loggerhead-instruments/amx/Arduino/amx/cmd.ino

#define CMD(a,b) ( a + (b << 8))
#define TRUE 1
#define FALSE 0

int ProcCmd(char *pCmd)
{
  short *pCV;
  short n;
  long lv1, lv2;
  char s[22];
        unsigned int tday;
        unsigned int tmonth;
        unsigned int tyear;
        unsigned int thour;
        unsigned int tmin;
        unsigned int tsec;

  pCV = (short*)pCmd;

  n = strlen(pCmd);
  if(n<2) 
          return TRUE;

  switch(*pCV)
  {                     
    // IMU
    case ('I' + ('M'<<8)):
    {
      sscanf(&pCmd[3],"%d",&lv1);
      imu_srate = lv1;
      fileType = 1;
      imuFlag = 1;
      break;
    }

  // Accelerometer full scale
    case ('A' + ('G'<<8)):
    {
      sscanf(&pCmd[3],"%d",&lv1);
      accel_scale = lv1;
      break;
    }

  // Hydrophone sensitivity if not default -180
    case ('H' + ('C'<<8)):
    {
      sscanf(&pCmd[3],"%d",&lv1);
      hydroCal = lv1;
      break;
    }

    // Keller Pressure and Temperature
    case ('K' + ('P'<<8)):
    {
      pressure_sensor = 2;
      fileType = 1;
      break;
    }

    // Measurement Specialities Pressure and Temperature
    case ('M' + ('P'<<8)):
    {
      pressure_sensor = 1;
      fileType = 1;
      break;
    }

    // RGB light sensor setup
    case ('L' + ('S'<<8)):
    {
      rgbFlag = 1;
      fileType = 1;
      break;
    }

    // Disable LEDs
    case ('L' + ('D'<<8)):
    {
      LEDSON = 0;
      break;
    }
    
    // Enable bright LED
    case ('B' + ('L'<<8)):
    {
      briteFlag = 1;
    }

    // Set of Real Time Clock
    case ('T' + ('M'<<8)):
    {
         //set time
         sscanf(&pCmd[3],"%d-%d-%d %d:%d:%d",&tyear,&tmonth,&tday,&thour,&tmin,&tsec);
         setTeensyTime(thour, tmin, tsec, tday, tmonth, tyear + 2000);
         Serial.print("Clock Set (now): ");
         Serial.println(now());
         Serial.print("Clock set (getTeensyTime): ");
         Serial.println(getTeensy3Time());
         break;
      }

    case ('B' + ('W'<<8)):
    {
         //set time
         sscanf(&pCmd[3],"%d-%d-%d %d:%d:%d",&tyear,&tmonth,&tday,&thour,&tmin,&tsec);
         tmElements_t NewTime;
         NewTime.Second = tsec;
         NewTime.Minute = tmin;
         NewTime.Hour = thour;
         NewTime.Day = tday;
         NewTime.Month = tmonth;
         NewTime.Year = tyear + 2000 - 1970;
         burnTime = makeTime(NewTime); // makeTime is offset from 1970
         burnFlag = 1;
         Serial.print("Burn Time:");
         Serial.println(burnTime);
         break;
      }

    // Burn Minutes (burn set number of minutes after start)
    case ('B' + ('M'<<8)):
    {
         sscanf(&pCmd[3],"%d",&lv1);
         burnMinutes = lv1;
         burnFlag = 2;
         break;
      }

      case ('N' + ('D'<<8)):
      {
        noDC = 1;
        break;
      }

    case ('D' + ('I'<<8)):
      {
        printDiags = 1;
        break;
      }
      
      case ('R' + ('D'<<8)):
      {
        sscanf(&pCmd[3],"%d",&lv1);
        rec_dur = lv1;
        break;
      }
      
      case ('R' + ('I'<<8)):
      {
        sscanf(&pCmd[3],"%d",&lv1);
        rec_int = lv1;
        break;
      } 

      case ('S' + ('G'<<8)):
      {
        sscanf(&pCmd[3],"%d",&lv1);
        systemGain = lv1;
        break;
      } 

    case ('D' + ('S'<<8)):
    {
      sscanf(&pCmd[3],"%d:%d",&lv1, &lv2);
      delayStartHours = lv1;
      delayStartMinutes = lv2;
      break;
    }  


    //default nPlayBackFiles = 0; // number of playback files
    case ('P' + ('F'<<8)):
    {
      sscanf(&pCmd[3],"%d",&lv1);
      nPlayBackFiles = lv1;
      break;
    }
    //default minPlayBackInterval = 120; // keep playbacks from being closer than x seconds
    case ('P' + ('I'<<8)):
    {
      sscanf(&pCmd[3],"%d",&lv1);
      minPlayBackInterval = lv1;
      break;
    }
    //default longestPlayback = 30; // longest file for playback, used to power down playback board
    case ('P' + ('D'<<8)):
    {
      sscanf(&pCmd[3],"%d",&lv1);
      longestPlayback = lv1;
      break;
    }
    //default playBackDepthThreshold = 10.0; // tag must go deeper than this depth to trigger threshold
    case ('P' + ('T'<<8)):
    {
      sscanf(&pCmd[3],"%d",&lv1);
      playBackDepthThreshold = lv1;
      break;
    }
    //default ascentDepthTrigger = 5.0; // after exceed playBackDepthThreshold, must ascend this amount to trigger playback
    case ('P' + ('A'<<8)):
    {
      sscanf(&pCmd[3],"%d",&lv1);
      ascentDepthTrigger = lv1;
      break;
    }
    //default playBackResetDepth = 2.0; // tag needs to come back above this depth before next playback can happen
    case ('P' + ('R'<<8)):
    {
      sscanf(&pCmd[3],"%d",&lv1);
      playBackResetDepth = lv1;
      break;
    }
    //default maxPlayBacks = 20; // tag needs to come back above this depth before next playback can happen
    case ('P' + ('M'<<8)):
    {
      sscanf(&pCmd[3],"%d",&lv1);
      maxPlayBacks = lv1;
      break;
    }
    // default simulateDepth = 0
    case ('S' + ('D'<<8)):
    {
      simulateDepth = 1;
      break;
    }
    
  } 
  return TRUE;
}

boolean LoadScript()
{
  char s[30];
  char c;
  short i;
  int j = 0;

  File file;
  unsigned long TM_byte;
  int comment_TM = 0;

  // Read card setup.txt file to set date and time, recording interval
  file=SD.open("setup.txt");
 if(file)
 {
   do{
        i = 0;
        s[i] = 0;
        do{
            c = file.read();
            if(c!='\r') s[i++] = c;
            if((c=='T') & (i==1)) 
            {
              TM_byte = file.position() - 1;
              comment_TM = 1;
            }
            if(i>29) break;
          }while(c!='\n');
          s[--i] = 0;
          if(s[0] != '/' && i>1)
          {
            ProcCmd(s);
          }
      }while(file.available());
      file.close();  
      
      // comment out TM line if it exists
      if (comment_TM)
      {
        Serial.print("Comment TM ");
        Serial.println(TM_byte);
        file = SD.open("setup.txt", FILE_WRITE);
        file.seek(TM_byte);
        file.print("//");
        file.close();
      }
      
  }
  else
  {   
    Serial.println("setup.txt not opened");

   // display.println("no setup file");
    return 0;
  }

  // Read simulated depth file
  file = SD.open("depth.txt");
  Serial.println("Depth file");
  if(file){
    do{
      j = 0;
      do{ // scan next line
        c = file.read();
        if(c!='\r') s[j] = c;
        j++;
        if(j>29) break;
      }while(c!='\n');
      Serial.print(c);
      sscanf(s,"%f",&depthProfile[i]);
      Serial.print(i); Serial.print(" ");
      Serial.print(depthProfile[i]);
      i++;
      if(i==60) break;
    }while(file.available());
    file.close();
  }
  
 return 1;  
}
