loggerhead-instruments/amx/Arduino/amx/ISL29125.ino

// Some code from Sparkfun  https://github.com/sparkfun/SparkFun_ISL29125_Breakout_Arduino_Library/tree/master/src

int _addr = 0x44;

// ISL29125 Registers
#define DEVICE_ID 0x00
#define CONFIG_1 0x01
#define CONFIG_2 0x02
#define CONFIG_3 0x03
#define THRESHOLD_LL 0x04
#define THRESHOLD_LH 0x05
#define THRESHOLD_HL 0x06
#define THRESHOLD_HH 0x07
#define STATUS 0x08 
#define GREEN_L 0x09 
#define GREEN_H 0x0A
#define RED_L 0x0B
#define RED_H 0x0C
#define BLUE_L 0x0D
#define BLUE_H 0x0E

// Configuration Settings
#define CFG_DEFAULT 0x00

// CONFIG1
// Pick a mode, determines what color[s] the sensor samples, if any
#define CFG1_MODE_POWERDOWN 0x00
#define CFG1_MODE_G 0x01
#define CFG1_MODE_R 0x02
#define CFG1_MODE_B 0x03
#define CFG1_MODE_STANDBY 0x04
#define CFG1_MODE_RGB 0x05
#define CFG1_MODE_RG 0x06
#define CFG1_MODE_GB 0x07

// Light intensity range
// In a dark environment 375Lux is best, otherwise 10KLux is likely the best option
#define CFG1_375LUX 0x00
#define CFG1_10KLUX 0x08

// Change this to 12 bit if you want less accuracy, but faster sensor reads
// At default 16 bit, each sensor sample for a given color is about ~100ms
#define CFG1_16BIT 0x00
#define CFG1_12BIT 0x10

// Unless you want the interrupt pin to be an input that triggers sensor sampling, leave this on normal
#define CFG1_ADC_SYNC_NORMAL 0x00
#define CFG1_ADC_SYNC_TO_INT 0x20

// CONFIG2
// Selects upper or lower range of IR filtering
#define CFG2_IR_OFFSET_OFF 0x00
#define CFG2_IR_OFFSET_ON 0x80

// Sets amount of IR filtering, can use these presets or any value between 0x00 and 0x3F
// Consult datasheet for detailed IR filtering calibration
#define CFG2_IR_ADJUST_LOW 0x00
#define CFG2_IR_ADJUST_MID 0x20
#define CFG2_IR_ADJUST_HIGH 0x3F

// CONFIG3
// No interrupts, or interrupts based on a selected color
#define CFG3_NO_INT 0x00
#define CFG3_G_INT 0x01
#define CFG3_R_INT 0x02
#define CFG3_B_INT 0x03

// How many times a sensor sample must hit a threshold before triggering an interrupt
// More consecutive samples means more times between interrupts, but less triggers from short transients
#define CFG3_INT_PRST1 0x00
#define CFG3_INT_PRST2 0x04
#define CFG3_INT_PRST4 0x08
#define CFG3_INT_PRST8 0x0C

// If you would rather have interrupts trigger when a sensor sampling is complete, enable this
// If this is disabled, interrupts are based on comparing sensor data to threshold settings
#define CFG3_RGB_CONV_TO_INT_DISABLE 0x00
#define CFG3_RGB_CONV_TO_INT_ENABLE 0x10

// STATUS FLAG MASKS
#define FLAG_INT 0x01
#define FLAG_CONV_DONE 0x02
#define FLAG_BROWNOUT 0x04
#define FLAG_CONV_G 0x10
#define FLAG_CONV_R 0x20
#define FLAG_CONV_B 0x30

bool islInit(){
  Serial.println("Light init"); 
  bool ret = true;
  ret = config(CFG1_MODE_RGB | CFG1_10KLUX, CFG2_IR_ADJUST_HIGH, CFG_DEFAULT); 
  return ret;
}

bool islSleep(){
  bool ret = true;
  ret = config(CFG1_MODE_POWERDOWN, CFG2_IR_ADJUST_HIGH, CFG_DEFAULT);
  return ret;
}

void islRead(){
  islRed = read16(RED_L);
  islGreen = read16(GREEN_L);
  islBlue = read16(BLUE_L);
}

// Generic I2C read register (single byte)
uint8_t read8(uint8_t reg)
{
  Wire.beginTransmission(_addr);
  Wire.write(reg);
  Wire.endTransmission();
  Wire.beginTransmission(_addr);
  Wire.requestFrom(_addr,(uint8_t)1);
  uint8_t data = Wire.read();
  Wire.endTransmission();
  
  return data;
}

uint16_t read16(uint8_t reg)
{
  uint16_t data = 0x0000;

  Wire.beginTransmission(_addr);
  Wire.write(reg);
  Wire.endTransmission();
  
  Wire.beginTransmission(_addr);
  Wire.requestFrom(_addr, (uint8_t)2); // request 2 bytes of data
  data = Wire.read();
  data |= (Wire.read() << 8);
  Wire.endTransmission();

  return data;
}

// Generic I2C write data to register (single byte)
void write8(uint8_t reg, uint8_t data)
{
  Wire.beginTransmission(_addr);
  Wire.write(reg);
  Wire.write(data);
  Wire.endTransmission();
  
  return;
}


bool config(uint8_t config1, uint8_t config2, uint8_t config3)
{
  bool ret = true;
  uint8_t data = 0x00;
  
  // Set 1st configuration register
  write8(CONFIG_1, config1);
  // Set 2nd configuration register
  write8(CONFIG_2, config2);
  // Set 3rd configuration register
  write8(CONFIG_3, config3);
  
  // Check if configurations were set correctly
  data = read8(CONFIG_1);
  if (data != config1)
  {
    ret &= false;
  }
  data = read8(CONFIG_2);
  if (data != config2)
  {
    ret &= false;
  }
  data = read8(CONFIG_3);
  if (data != config3)
  {
    ret &= false;
  }
  return ret;
}
