loggerhead-instruments/amx/Arduino/amx/i2cFunc.ino

// i2c functions for Teensy 3.x i2c_t3 library


void readBytes(uint8_t address, uint8_t subAddress, uint8_t count, volatile uint8_t * dest)
{  
  Wire.beginTransmission(address);   // Initialize the Tx buffer
  Wire.write(subAddress);            // Put slave register address in Tx buffer
//  Wire.endTransmission(I2C_NOSTOP);  // Send the Tx buffer, but send a restart to keep connection alive
  Wire.endTransmission(false);       // Send the Tx buffer, but send a restart to keep connection alive
  uint8_t i = 0;
//        Wire.requestFrom(address, count);  // Read bytes from slave register address 
        Wire.requestFrom(address, (size_t) count);  // Read bytes from slave register address 
  while (Wire.available()) {
        dest[i++] = Wire.read(); }         // Put read results in the Rx buffer
}
