loggerhead-instruments/amx/Arduino/amx/euler.ino

// simple calculation of pitch, roll, yaw
void euler(){
  
  mag_x -= magXoffset;
  mag_y -= magYoffset;
  mag_z -= magZoffset;
  
  // roll
  float phi = atan2(accel_y, accel_z); // roll in radians

  // de-rotate by roll angle
  float sinAngle = sin(phi);
  float cosAngle = cos(phi);
  float Bfy = (mag_y * cosAngle) - (mag_z * sinAngle);
  float Bz = (mag_y * sinAngle) + (mag_z * cosAngle);
  float Gz = (accel_y * sinAngle) + (accel_z * cosAngle);

  // theta = pitch angle
  float theta = atan(- accel_x / Gz);
  sinAngle = sin(theta);
  cosAngle = cos(theta);

  // de-rotate by pitch angle theta
  float Bfx = (mag_x * cosAngle) + (Bz * sinAngle);
  float Bfz = (-mag_x * sinAngle) + (Bz * cosAngle);

  // Psi = yaw = heading
  float psi = atan2(-Bfy, Bfx);

  pitch = degrees(theta);
  roll = degrees(phi);
  yaw = degrees(psi);
}
